ak66666/ThumbsUpV6Rp2040MX/Photos/IMG_20230707_214746391.jpg

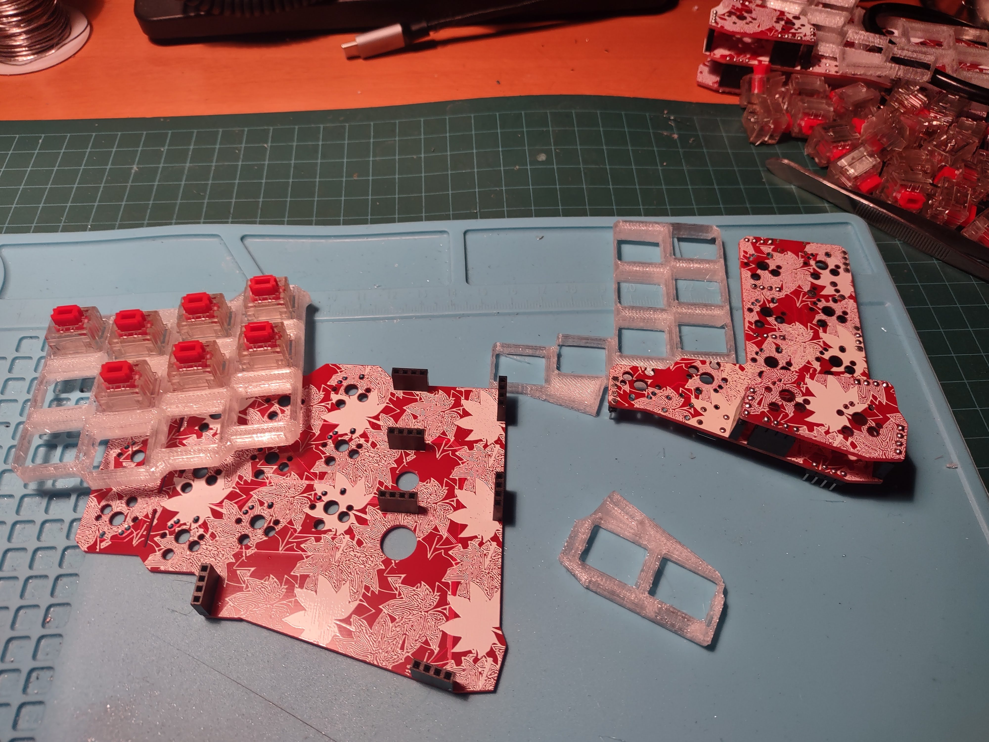
Photos/IMG_20230707_214746391.jpg
