ak66666/ThumbsUpV6Rp2040MX/Photos/IMG_20230707_214856131.jpg

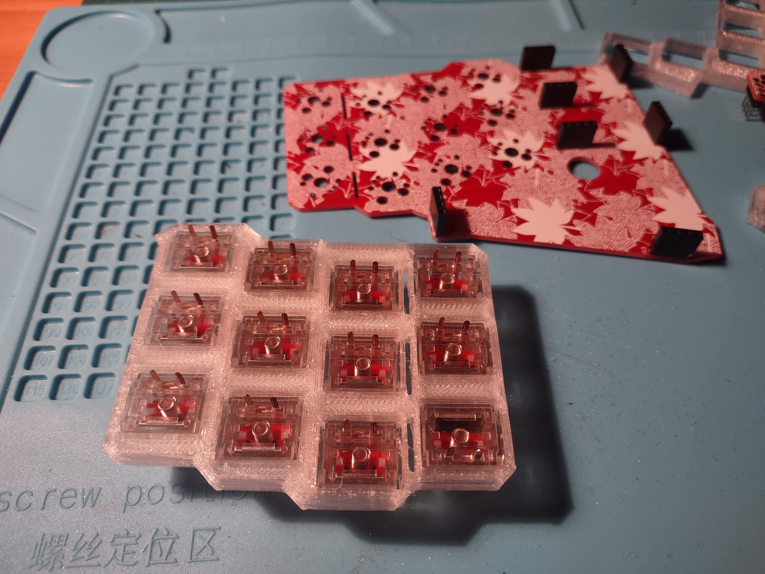
Photos/IMG_20230707_214856131.jpg
