ak66666/ThumbsUpV6Rp2040MX/Photos/IMG_20230707_222940790.jpg

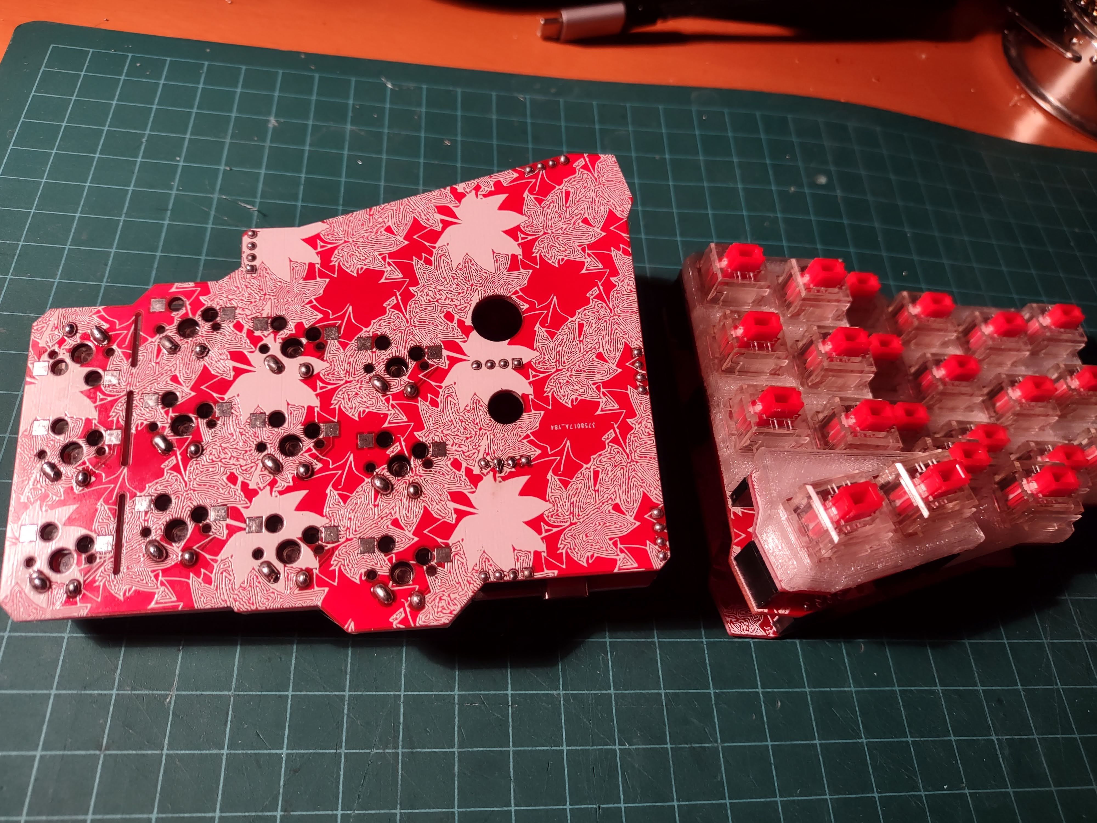
Photos/IMG_20230707_222940790.jpg
