ak66666/ThumbsUpV6Rp2040MX/Photos/IMG_20230707_223950950.jpg

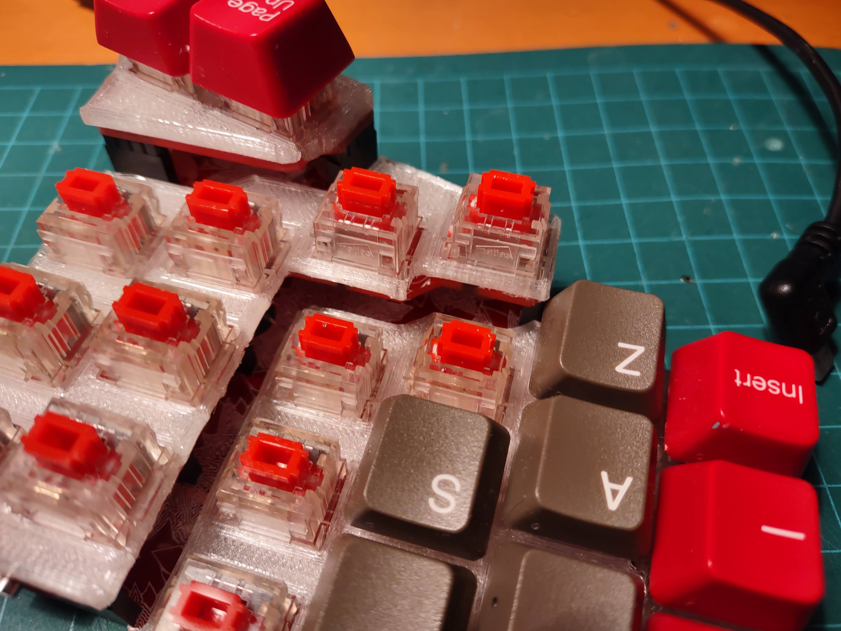
Photos/IMG_20230707_223950950.jpg
