ak66666/ThumbsUpV6Rp2040MX/Photos/IMG_20230707_224344655.jpg

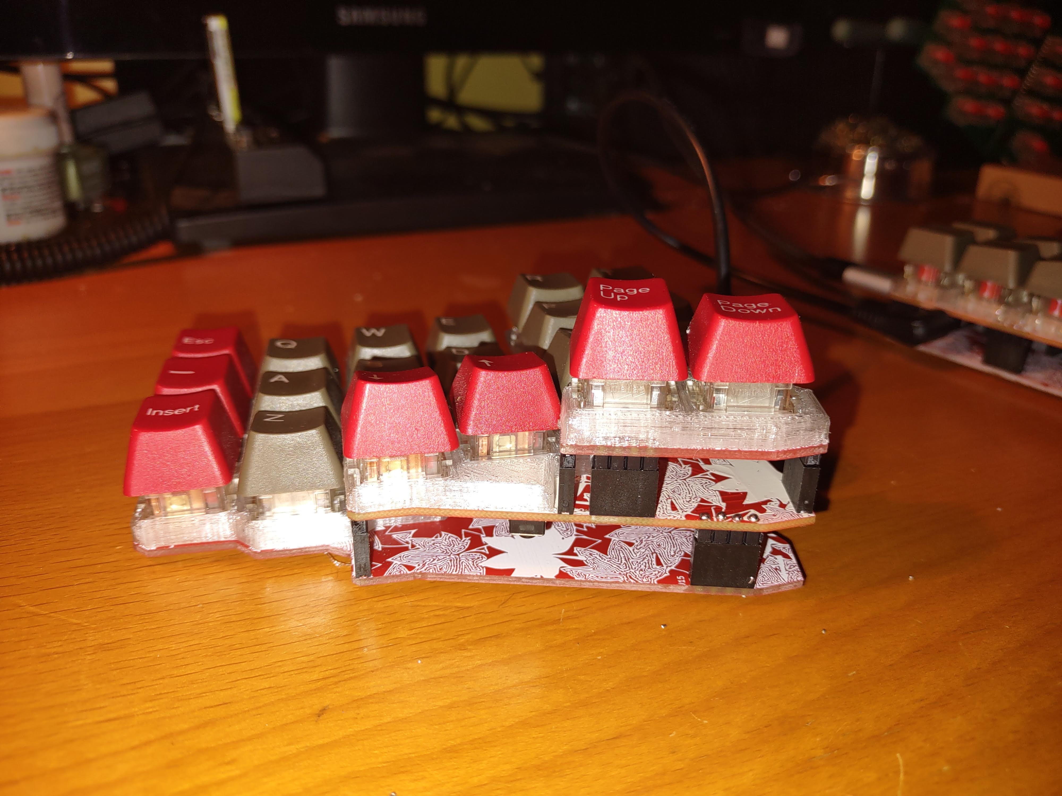
Photos/IMG_20230707_224344655.jpg
