ak66666/ThumbsUpV6Rp2040MX/Photos/IMG_20230811_215237122_HDR.jpg

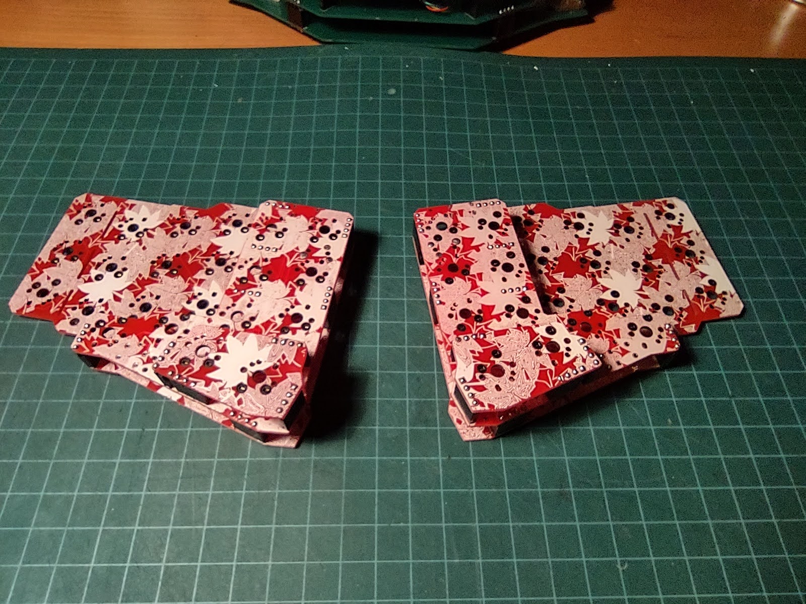
Photos/IMG_20230811_215237122_HDR.jpg
