ak66666/ThumbsUpV6Rp2040MX/Photos/IMG_20230811_215304264.jpg

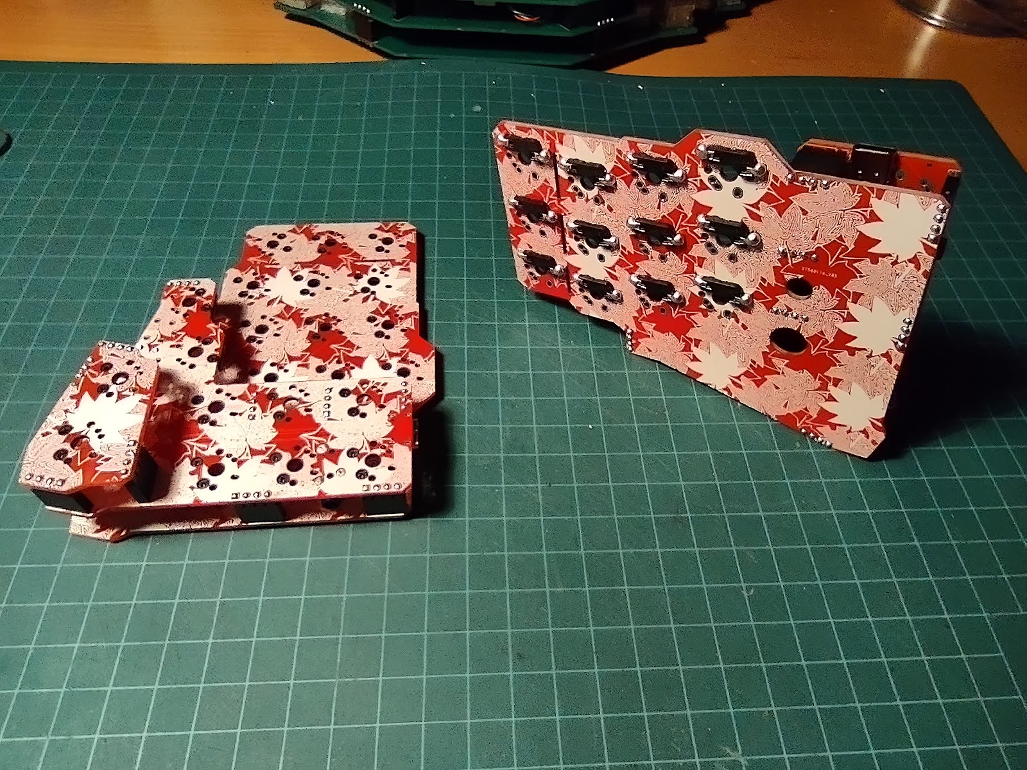
Photos/IMG_20230811_215304264.jpg
