ak66666/ThumbsUpV6Rp2040MX/Photos/IMG_20230811_215339513.jpg

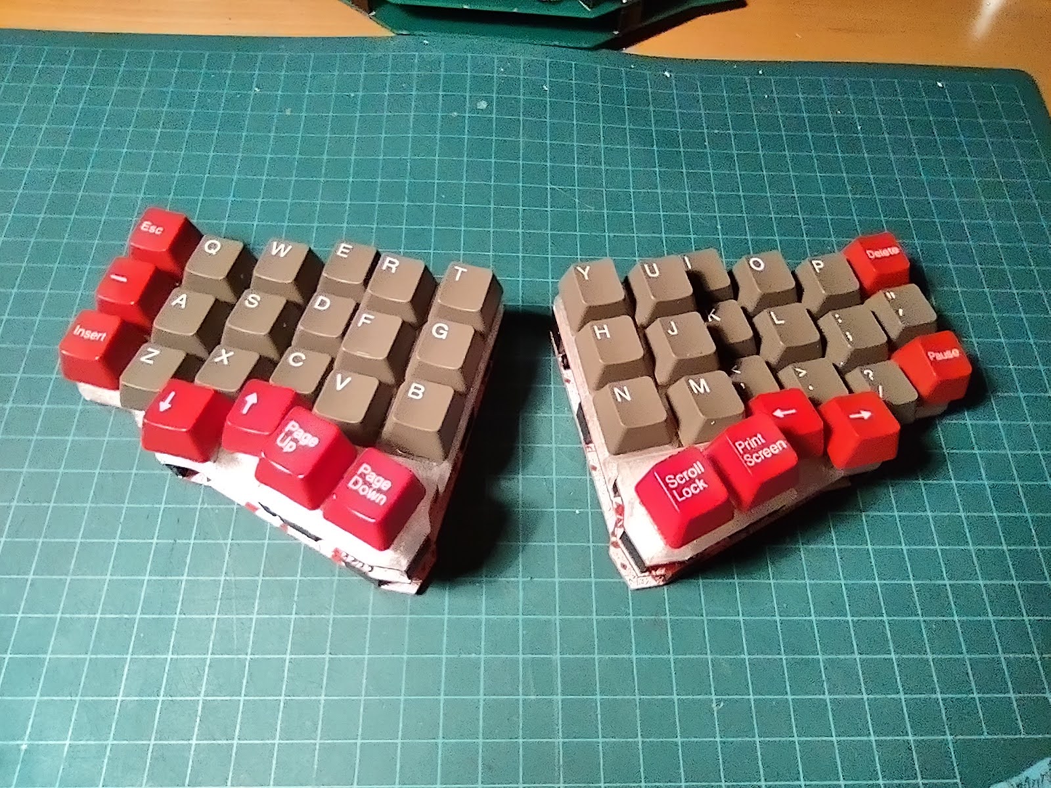
Photos/IMG_20230811_215339513.jpg
