ak66666/ThumbsUpV6Rp2040MX/Photos/IMG_20230811_215349415.jpg

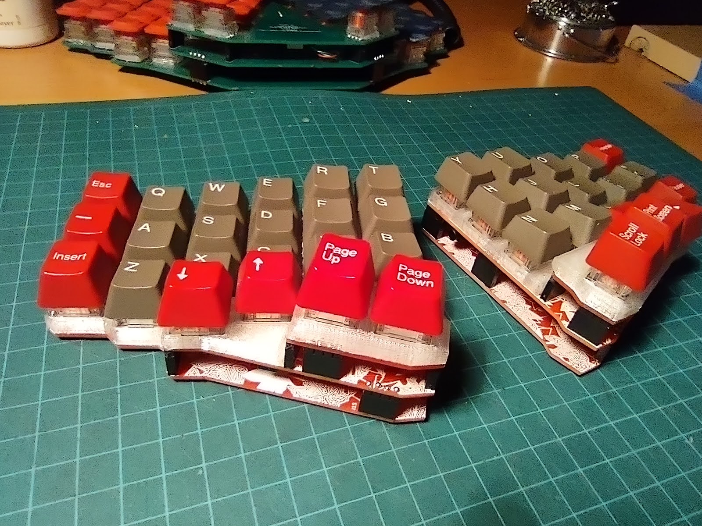
Photos/IMG_20230811_215349415.jpg
