ak66666/ThumbsUpV6Rp2040MX/Photos/IMG_20230811_224108562.jpg

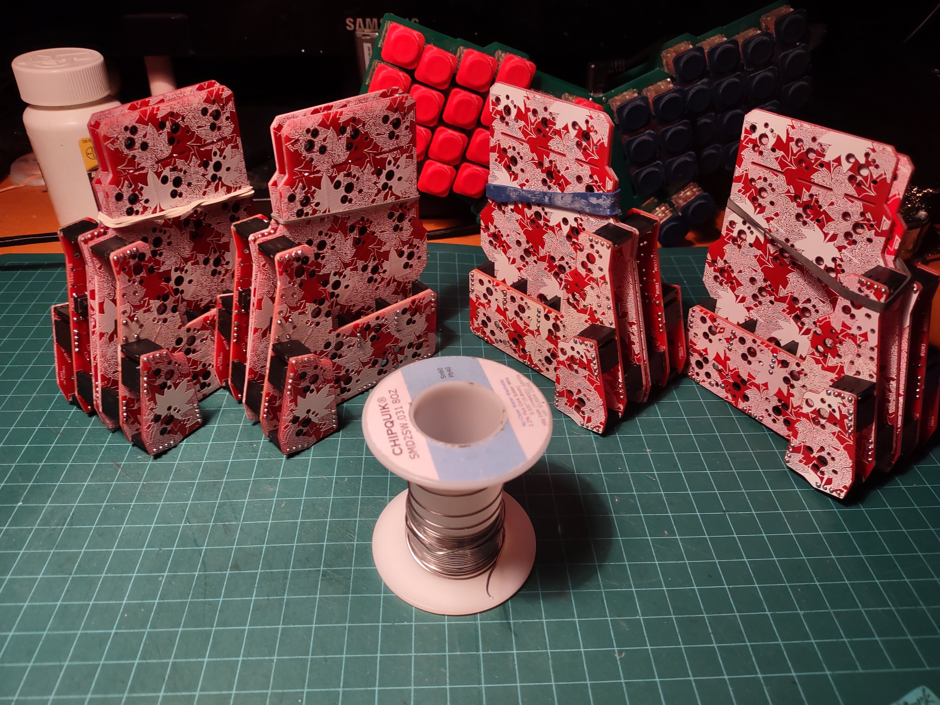
Photos/IMG_20230811_224108562.jpg
