ak66666/ThumbsUpV6Rp2040MX/Photos/IMG_20230811_224651306.jpg

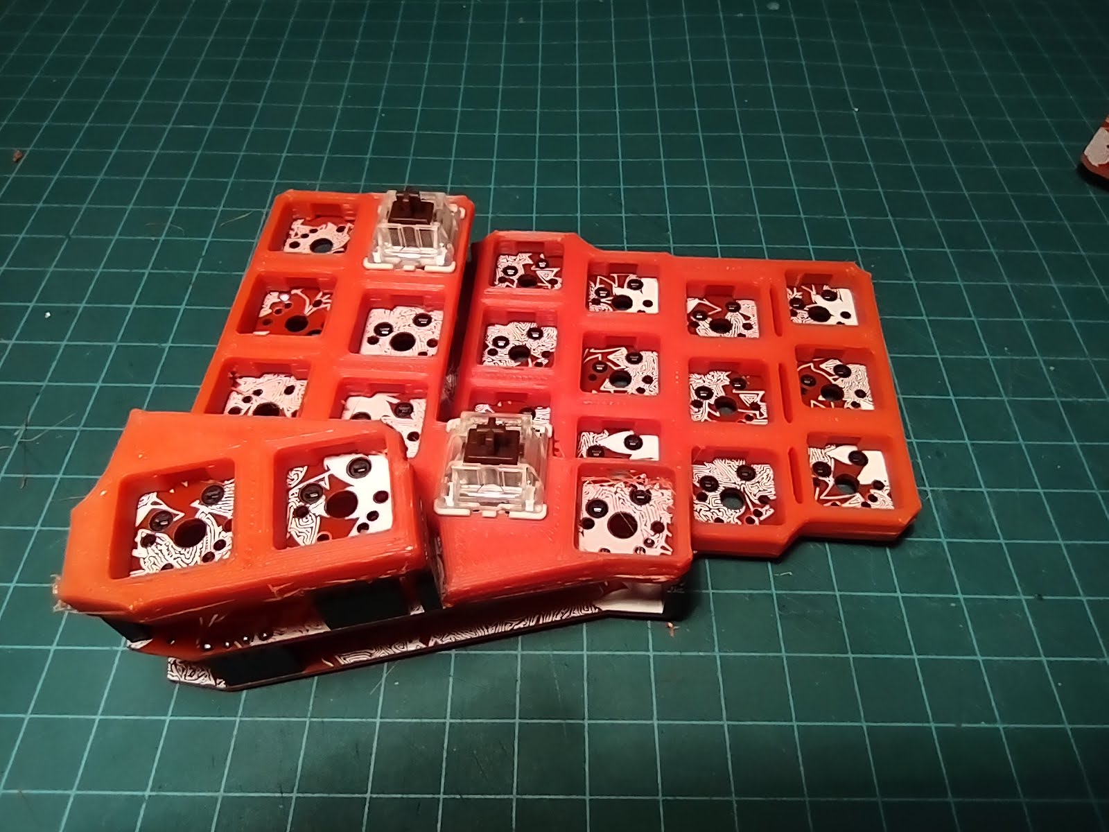
Photos/IMG_20230811_224651306.jpg
