ak66666/ThumbsUpV6Rp2040MX/Photos/IMG_20230812_205831370.jpg

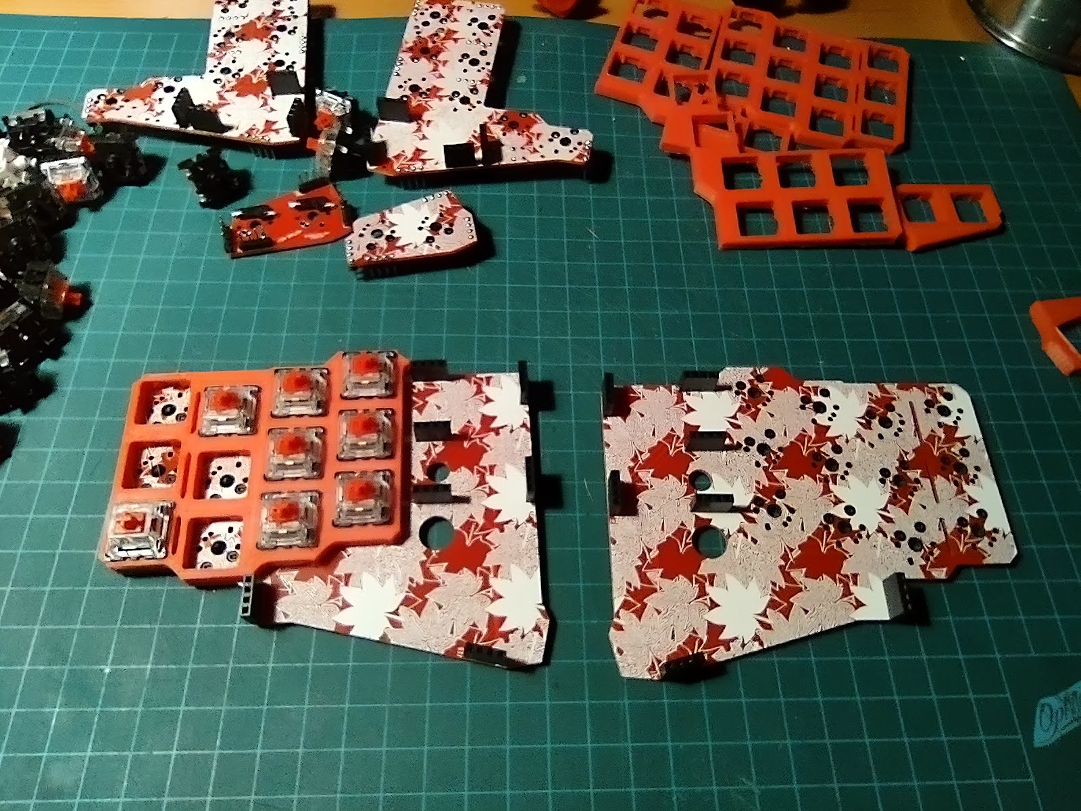
Photos/IMG_20230812_205831370.jpg
