ak66666/ThumbsUpV6Rp2040MX/Photos/IMG_20230812_210523874.jpg

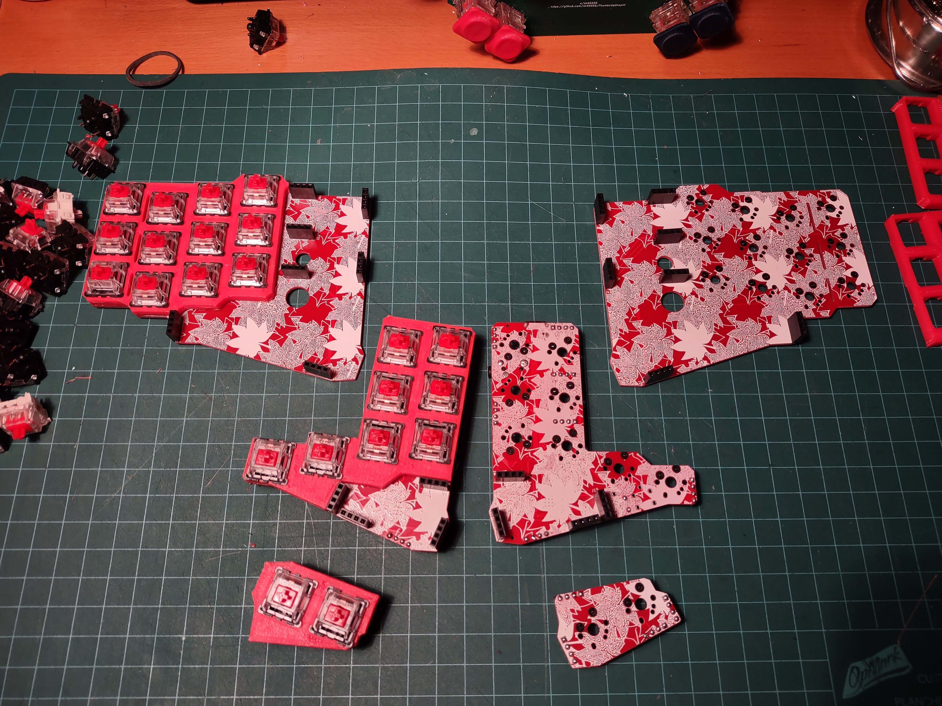
Photos/IMG_20230812_210523874.jpg
