ak66666/ThumbsUpV6Rp2040MX/Photos/IMG_20230812_211328677.jpg

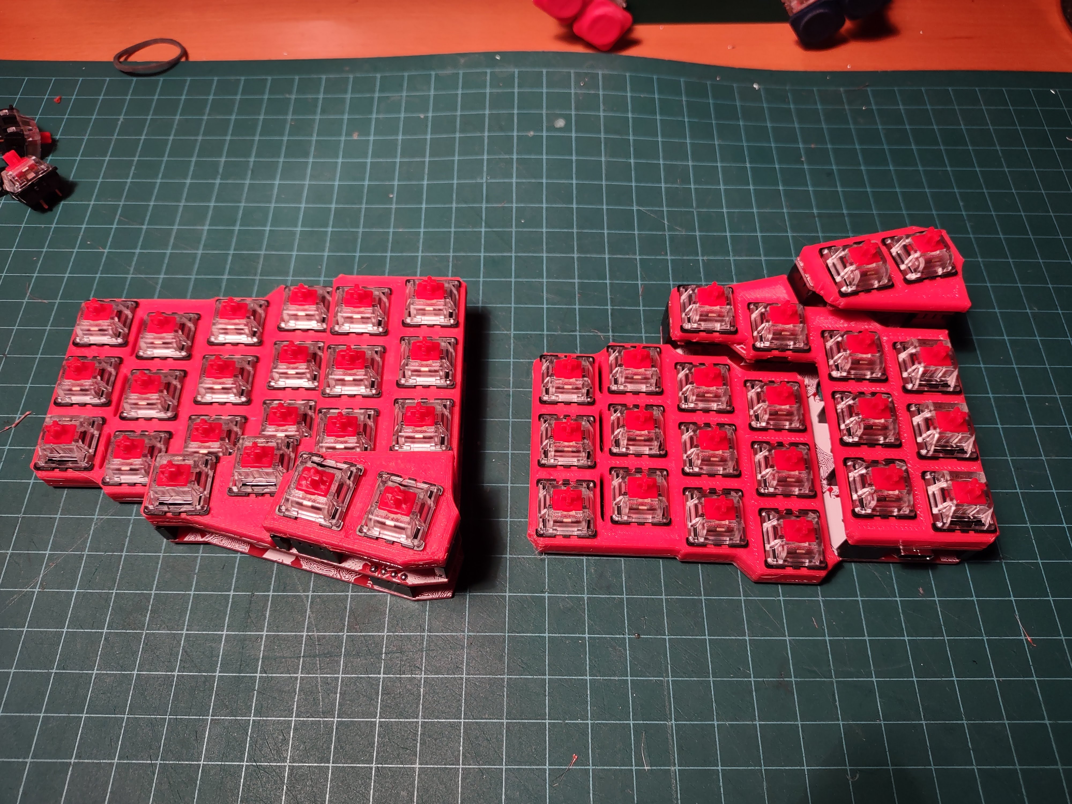
Photos/IMG_20230812_211328677.jpg
