ak66666/ThumbsUpV6Rp2040MX/Photos/IMG_20230812_211406796.jpg

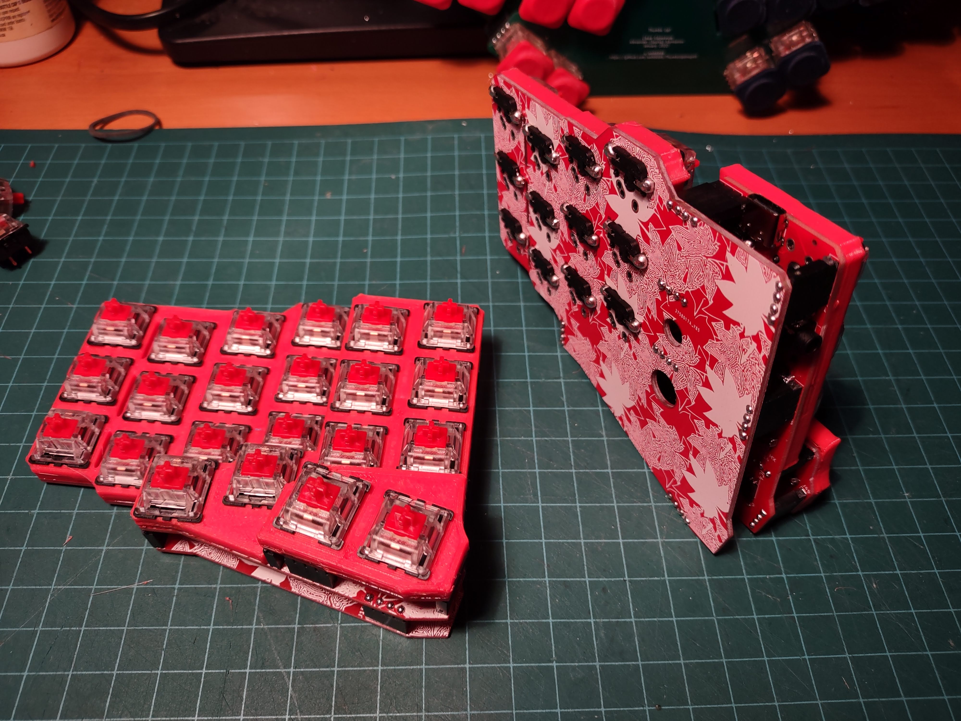
Photos/IMG_20230812_211406796.jpg
