ak66666/ThumbsUpV6Rp2040MX/Photos/IMG_20230814_161242132_HDR.jpg

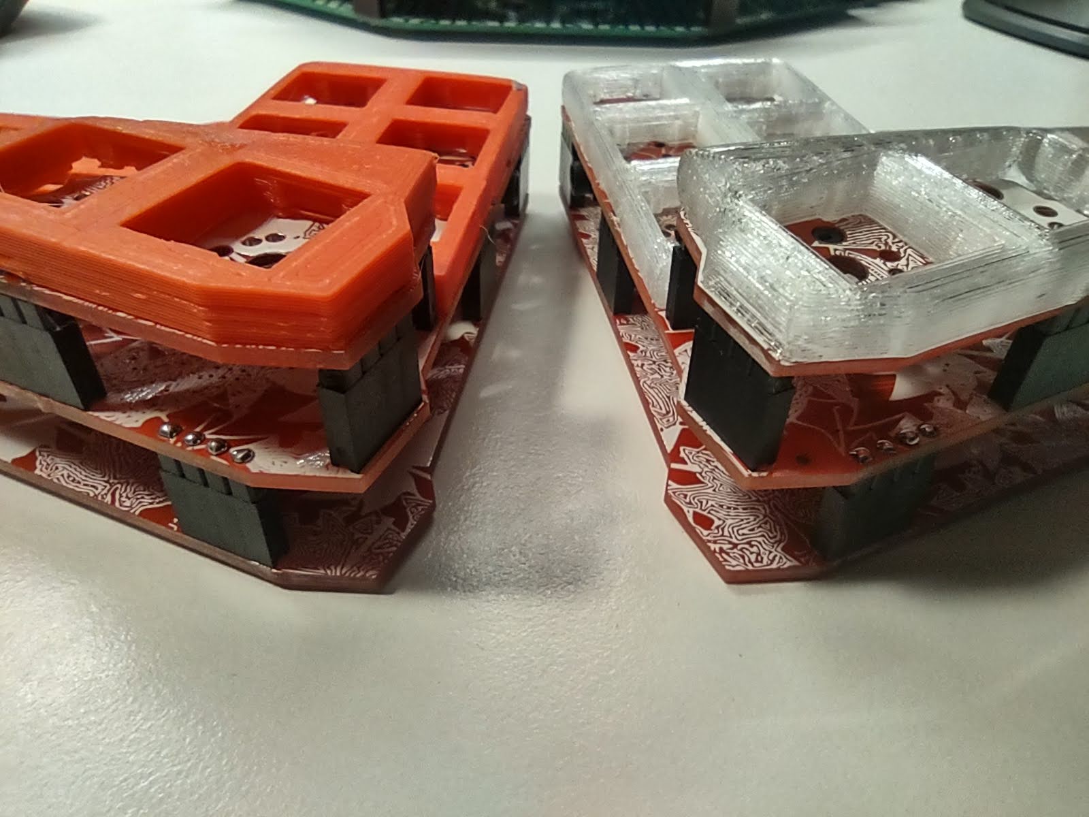
Photos/IMG_20230814_161242132_HDR.jpg
