ak66666/ThumbsUpV6Rp2040MX/Photos/IMG_20230818_104519609_HDR.jpg

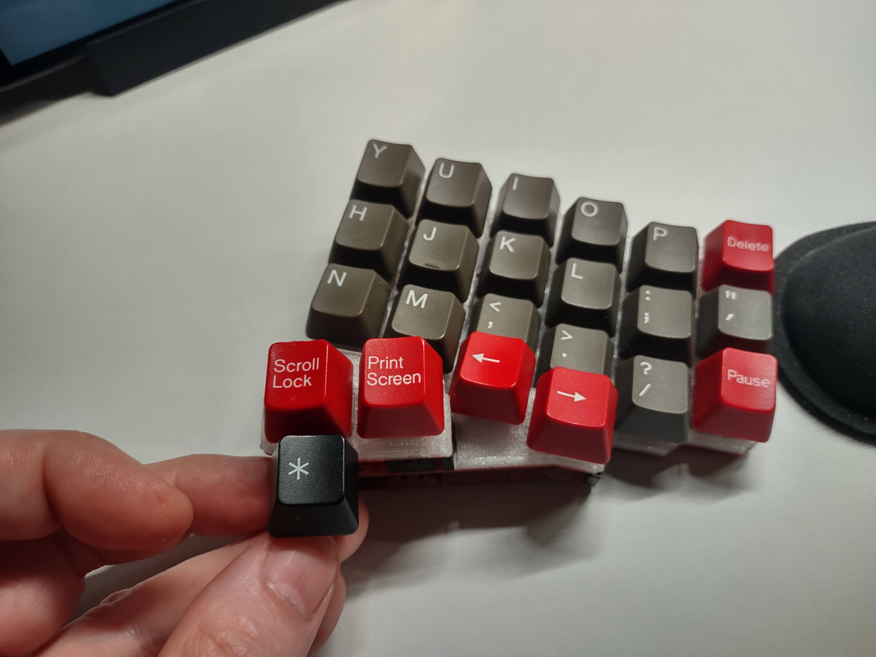
Photos/IMG_20230818_104519609_HDR.jpg
