ak66666/ThumbsUpV6Rp2040MX/Silkscreens/Leaves.bmp

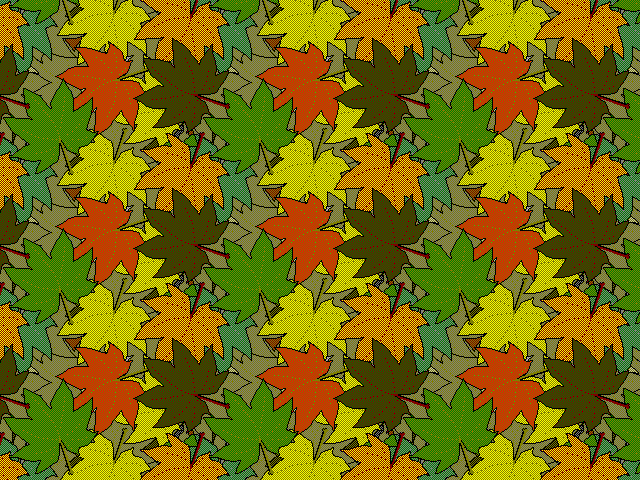
Silkscreens/Leaves.bmp
