ak66666/ThumbsUpV6Rp2040MX/ThumbsUp 2.step

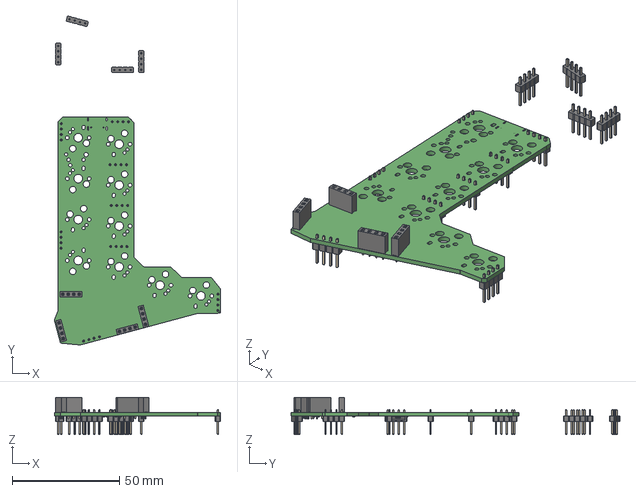
[picture p65: CAD file, 2023-06-15]
ThumbsUp 2.step
77.5 x 153.2 x 17.2 mm
