ak66666/ThumbsUpV6Rp2040MX/Outline.dxf

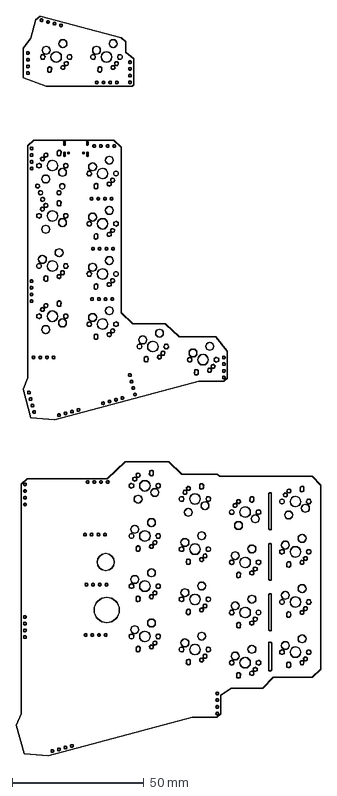
[picture p66: CAD file, 2023-06-15]
Outline.dxf
115.4 x 280.8 mm
