ak66666/ThumbsUpV6Rp2040MX/105450-0101/3D/105450-0101.stp

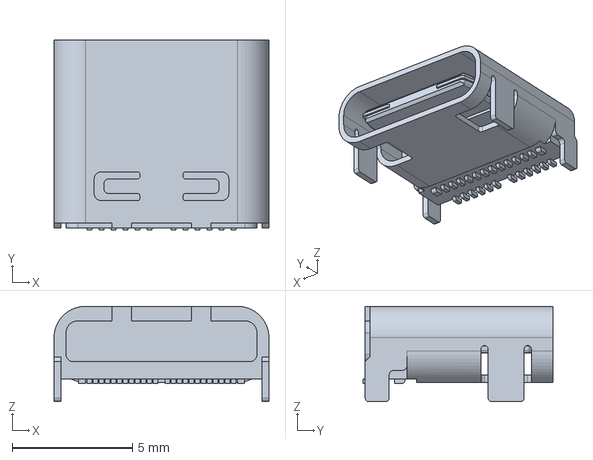
[picture p67: CAD file, 2023-06-15]
105450-0101/3D/105450-0101.stp
8.94 x 7.90 x 3.96 mm
